kellertk/PICclock/src/freq_table.h

/**
 * freq_table.h - Combined frequency lookup table
 * 
 * Maps ADC values (0-255) to frequency settings for the PIC16F18344.
 * Smooth logarithmic sweep from 1 Hz to 1 MHz - no jumps at mode transitions.
 * 
 * Two modes (transparent to user):
 *   - Software mode (1-11 Hz): Delay loops, table contains half-period cycles
 *   - NCO mode (12+ Hz): Hardware NCO, table contains NCO increment
 * 
 * Bit 31 indicates mode:
 *   - Bit 31 = 0: NCO mode, lower 20 bits = NCO increment value
 *   - Bit 31 = 1: Software mode, lower 24 bits = half-period in cycles
 * 
 * Frequency formula: freq[i] = exp(i * ln(1000000) / 255)
 * Step ratio: 5.57% per index (smooth logarithmic progression)
 * 
 * NCO FDC mode: Output toggles on each accumulator overflow, so:
 *   F_out = (24 MHz x NCO_INC) / 2^21
 * Software: F_out = 24 MHz / (2 x half_period_cycles)
 */

#ifndef FREQ_TABLE_H
#define FREQ_TABLE_H

#include <stdint.h>

#define FREQ_MODE_SOFTWARE  0x80000000UL
#define FREQ_MODE_MASK      0x80000000UL
#define FREQ_VALUE_MASK     0x00FFFFFFUL

#define IS_SOFTWARE_MODE(x) ((x) & FREQ_MODE_MASK)
#define GET_FREQ_VALUE(x)   ((x) & FREQ_VALUE_MASK)

/**
 * Frequency table: 256 entries, logarithmic 1 Hz to 1 MHz
 * 
 * freq[i] = exp(i * ln(1000000) / 255) Hz
 * 
 * Software mode (i=0-44): half_period = 12000000 / freq  (cycles @ 24 MHz)
 * NCO mode (i=45-255): nco_inc = freq * 2097152 / 24000000
 * 
 * Crossover at index 45: ~11.4 Hz (NCO minimum with increment=1 = 11.44 Hz)
 */
static const uint32_t freq_table[256] = {
    // Index 0-44: Software mode (1 Hz to 11 Hz)
    // Value = 0x80000000 | half_period_cycles
    0x80B71B00,  //   0:    1.00 Hz
    0x80AD72F4,  //   1:    1.06 Hz
    0x80A44D47,  //   2:    1.11 Hz
    0x809BA318,  //   3:    1.18 Hz
    0x80936DE4,  //   4:    1.24 Hz
    0x808BA77F,  //   5:    1.31 Hz
    0x80844A12,  //   6:    1.38 Hz
    0x807D5014,  //   7:    1.46 Hz
    0x8076B445,  //   8:    1.54 Hz
    0x807071AF,  //   9:    1.63 Hz
    0x806A839E,  //  10:    1.72 Hz
    0x8064E59B,  //  11:    1.81 Hz
    0x805F936E,  //  12:    1.92 Hz
    0x805A8917,  //  13:    2.02 Hz
    0x8055C2CD,  //  14:    2.14 Hz
    0x80513CF9,  //  15:    2.25 Hz
    0x804CF434,  //  16:    2.38 Hz
    0x8048E546,  //  17:    2.51 Hz
    0x80450D22,  //  18:    2.65 Hz
    0x804168E5,  //  19:    2.80 Hz
    0x803DF5D2,  //  20:    2.96 Hz
    0x803AB151,  //  21:    3.12 Hz
    0x803798ED,  //  22:    3.29 Hz
    0x8034AA53,  //  23:    3.48 Hz
    0x8031E34F,  //  24:    3.67 Hz
    0x802F41CA,  //  25:    3.87 Hz
    0x802CC3CA,  //  26:    4.09 Hz
    0x802A676F,  //  27:    4.32 Hz
    0x80282AF3,  //  28:    4.56 Hz
    0x80260CA9,  //  29:    4.81 Hz
    0x80240AF7,  //  30:    5.08 Hz
    0x8022245D,  //  31:    5.36 Hz
    0x8020576C,  //  32:    5.66 Hz
    0x801EA2CB,  //  33:    5.98 Hz
    0x801D0530,  //  34:    6.31 Hz
    0x801B7D65,  //  35:    6.66 Hz
    0x801A0A43,  //  36:    7.03 Hz
    0x8018AAB4,  //  37:    7.42 Hz
    0x80175DB0,  //  38:    7.84 Hz
    0x8016223B,  //  39:    8.27 Hz
    0x8014F769,  //  40:    8.73 Hz
    0x8013DC59,  //  41:    9.22 Hz
    0x8012D037,  //  42:    9.73 Hz
    0x8011D239,  //  43:   10.27 Hz
    0x8010E1A0,  //  44:   10.85 Hz
    
    // Index 45-255: NCO mode (11 Hz to 1 MHz)
    // Value = NCO increment (20-bit)
             1,  //  45:      11 Hz
             1,  //  46:      12 Hz
             1,  //  47:      13 Hz
             1,  //  48:      13 Hz
             1,  //  49:      14 Hz
             1,  //  50:      15 Hz
             1,  //  51:      16 Hz
             1,  //  52:      17 Hz
             2,  //  53:      18 Hz
             2,  //  54:      19 Hz
             2,  //  55:      20 Hz
             2,  //  56:      21 Hz
             2,  //  57:      22 Hz
             2,  //  58:      23 Hz
             2,  //  59:      24 Hz
             2,  //  60:      26 Hz
             2,  //  61:      27 Hz
             3,  //  62:      29 Hz
             3,  //  63:      30 Hz
             3,  //  64:      32 Hz
             3,  //  65:      34 Hz
             3,  //  66:      36 Hz
             3,  //  67:      38 Hz
             3,  //  68:      40 Hz
             4,  //  69:      42 Hz
             4,  //  70:      44 Hz
             4,  //  71:      47 Hz
             4,  //  72:      49 Hz
             5,  //  73:      52 Hz
             5,  //  74:      55 Hz
             5,  //  75:      58 Hz
             5,  //  76:      61 Hz
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
    0x8012B5DC,  //  39:    9.79 Hz
    0x8011A5C0,  //  40:   10.38 Hz
    0x8010A51A,  //  41:   11.00 Hz
    // Index 42-255: NCO mode (12 Hz to 3 MHz)
             1,  //  42:      12 Hz
             ...
        262144,  // 255: 3000000 Hz
};
*/

#endif // FREQ_TABLE_H
